Mery-R/Engineering_Thesis/docs/Images/IMG_20260111_221652127.jpg

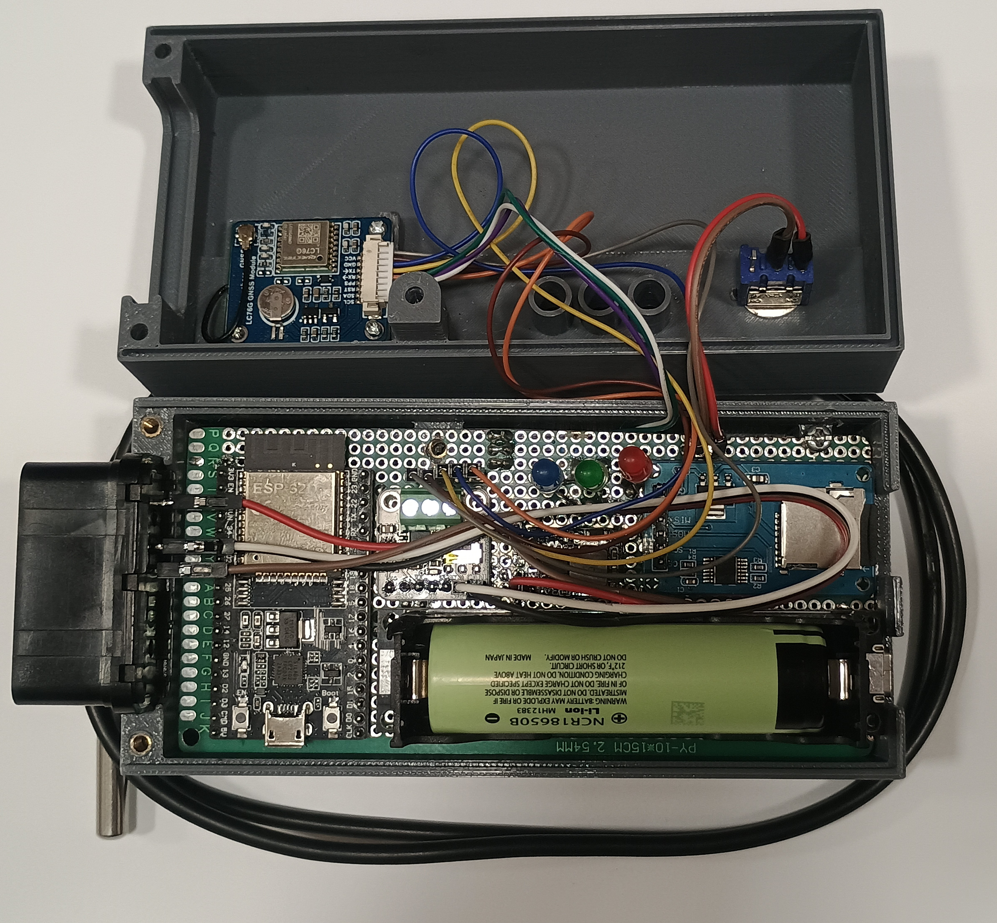
docs/Images/IMG_20260111_221652127.jpg
